angelisidro/BalamBoard21/hardware/4.PNG

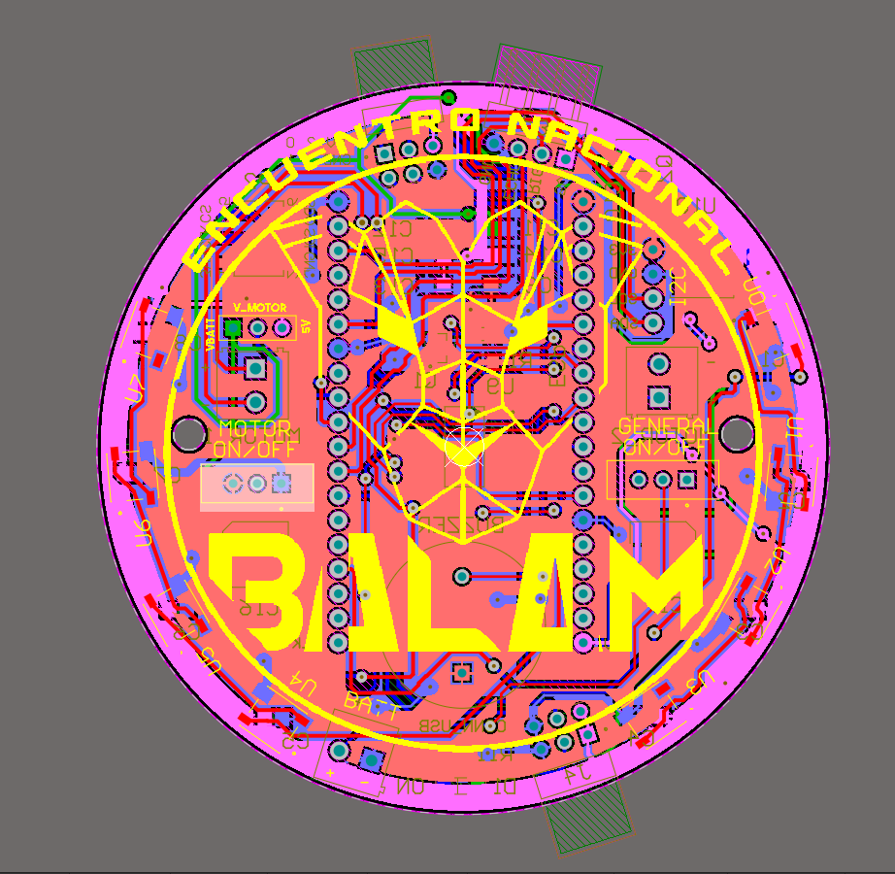
hardware/4.PNG
